kaustubhdoval/ESP-Spotify-Player/src/secrets_EXAMPLE.h

// USE THIS FILE AS A TEMPLATE FOR YOUR OWN secrets.h FILE
#ifndef SECRETS_H
#define SECRETS_H

// WiFi credentials
#define WIFI_SSID "WifiNetworkName"
#define PASSWORD "WifiPassword"

// Spotify API credentials
#define CLIENT_ID "SpotifyClientID"
#define CLIENT_SECRET "SpotifyClientSecret"
#define REDIRECT_URI "SpotifyRedirectURI"

// Timing constants
#define API_REFRESH_INTERVAL 5000 // 5 seconds
#define VOLUME_UPDATE_THRESHOLD 2 // Minimum volume change to update

#endif
